MattisLind/HP2116_regulators/Powerup_and_voltage_monitor.asc

C1: cap; 330µ
D1: diode; 1N4148
D2: diode; 1N4148
D3: diode; 1N4148
D4: diode; 1N4148
D5: zener; BZX84B18VL
D6: diode; 1N4148
D7: zener; BZX84B6V8L
D8: diode; 1N4148
D9: zener; BZX84C16VL
D10: diode; 1N4148
Q1: pnp; 2N3906
Q2: pnp; 2N3906
Q3: npn; 2N3904
Q4: pnp; 2N3906
Q5: pnp; 2N3906
Q6: npn; 2N3904
Q7: pnp; 2N3906
Q8: pnp; 2N3906
Q9: pnp; 2N3906
Q10: npn; 2N3904
Q11: pnp; 2N3906
R1: Res; 2200
R2: Res; 470
R3: Res; 4700
R4: Res; 2200
R5: Res; 220
R6: Res; 1000
R7: res; 47.5
R8: Res; 470
R9: Res; 4700
R10: Res; 2200
R11: Res; 1k
R12: Res; 10k
R13: Res; 1.5k
R14: Res; 1k
R15: Res; 1k
R16: Res; 2200
R17: Res; 4700
R18: Res; 499
R19: Res; 2200
R20: Res; 4700
R21: Res; 2200
R22: Res; 4700
R24: res; 220
R25: Res; 1000
R26: Res; 1000
R27: Res; 18k
R28: Res; 5.6k
R29: Res; 1000
V1: voltage; PULSE(0 4.5 0 10m 0 10 1 1)
V2: voltage; PULSE(0 2 0 10ms 0 5 10 1)
V3: voltage; PULSE(0 32 200m 10m 10m 2 4 2)
V4: voltage; PULSE(0 12 0 10m 0 10 1 1)
V5: voltage; PULSE(0 22 0 10m 0 10 1 1)
V6: voltage; PULSE(0 4.5 100m 100n 100n 5 10 2)
V7: voltage; PULSE(0 22 0 10m 0 10 1 1)
Named nets: 0
.tran 10000ms
